LTTJ/Projekt-Omega/Hardware/Home/DXF/wood_roof_front.dxf

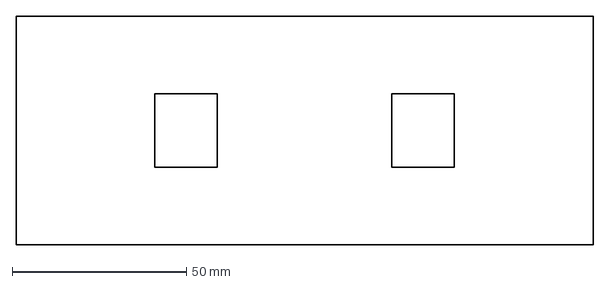
[picture p15: CAD file, 2021-09-07]
Hardware/Home/DXF/wood_roof_front.dxf
165.5 x 65.5 mm
