LTTJ/Projekt-Omega/Hardware/Home/DXF/wood_left.dxf

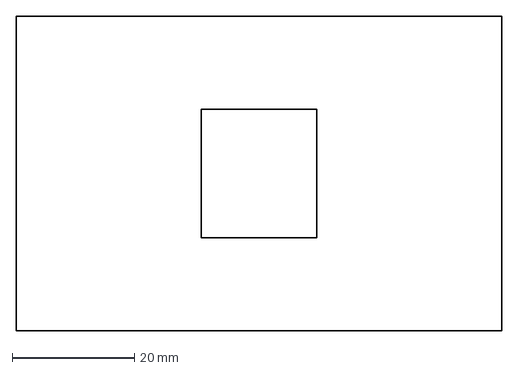
[picture p16: CAD file, 2021-09-07]
Hardware/Home/DXF/wood_left.dxf
79.5 x 51.5 mm
