LTTJ/Projekt-Omega/Hardware/Home/STL/roof.stl

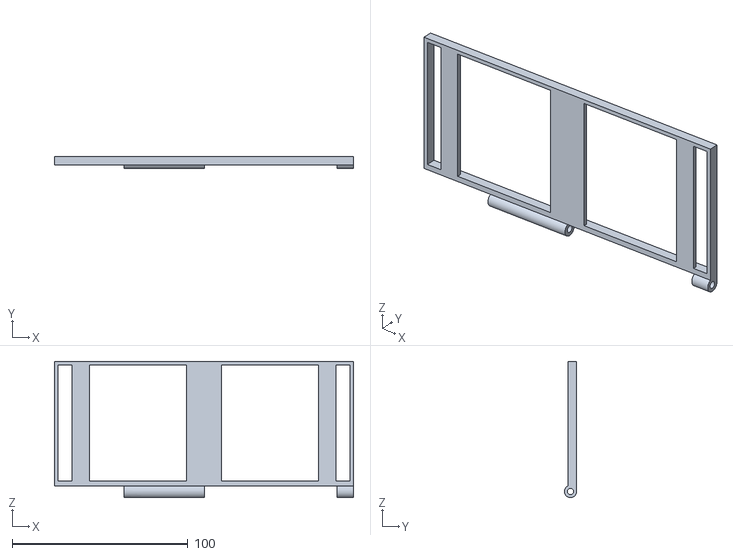
[picture p17: CAD file, 2021-09-07]
Hardware/Home/STL/roof.stl
170.0 x 7.00 x 77.5
