LTTJ/Projekt-Omega/Hardware/Home/DXF/wood_roof_back.dxf

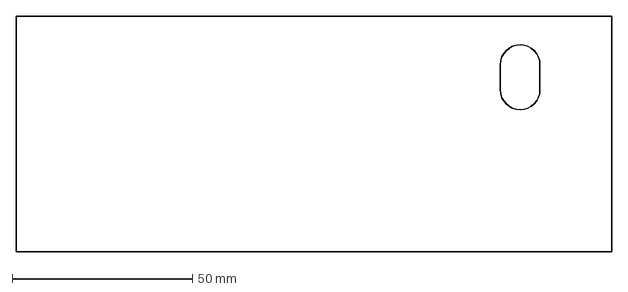
[picture p18: CAD file, 2021-09-07]
Hardware/Home/DXF/wood_roof_back.dxf
165.5 x 65.5 mm
