LTTJ/Projekt-Omega/Hardware/Home/STL/chimney.stl

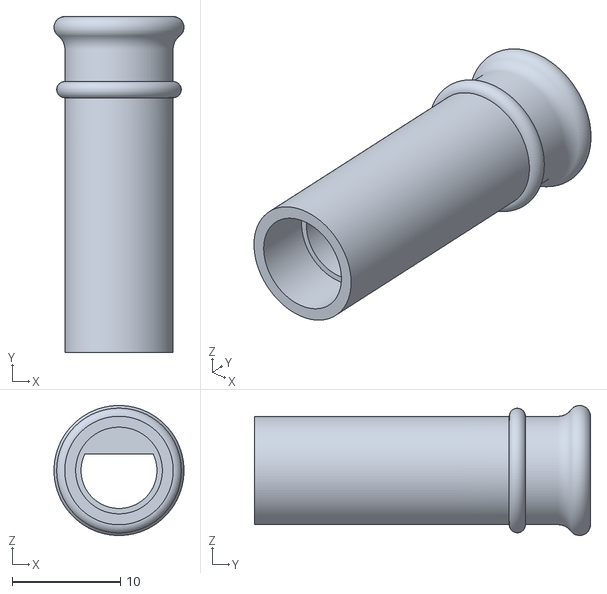
[picture p19: CAD file, 2021-09-07]
Hardware/Home/STL/chimney.stl
12.0 x 31.0 x 12.0
