LTTJ/Projekt-Omega/Hardware/Home/DXF/wood_roof_left.dxf

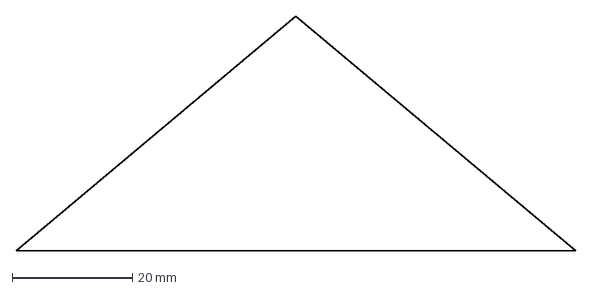
[picture p20: CAD file, 2021-09-07]
Hardware/Home/DXF/wood_roof_left.dxf
93.0 x 39.0 mm
