LTTJ/Projekt-Omega/Software/Arduino/OutdoorHouse/secrets_example.h

const char broker[] = "URL";
const int port = 1234;
const char username[] = "username";
const char password[] = "password";

// mit dem folgenden Befehl kann in der Kosole überprüft werden, ob die Daten auch übermittelt werden.
// mosquitto_sub -h URL -p PORT -u USERNAME -P PASSWORD -t TOPIC
